TampaHackerspace/SuperHoop/code/SuperHoop_PCB/20131002_133155.jpg

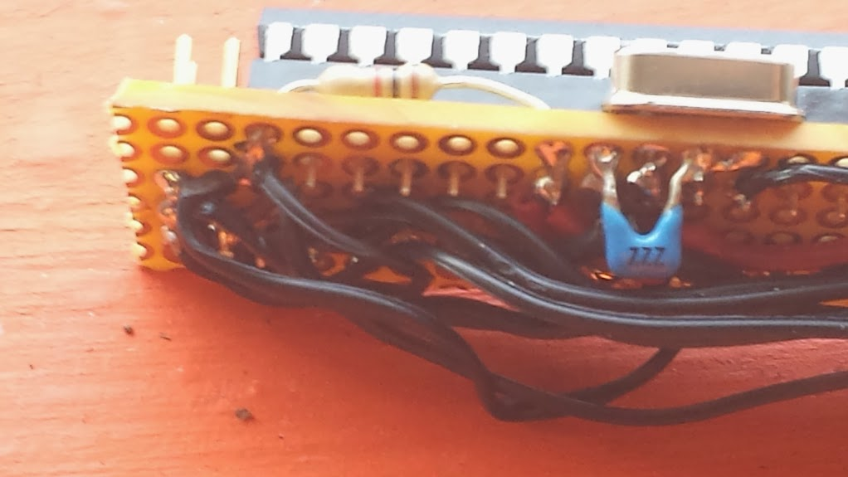
code/SuperHoop_PCB/20131002_133155.jpg
