TampaHackerspace/SuperHoop/code/SuperHoop_PCB/20131002_133200.jpg

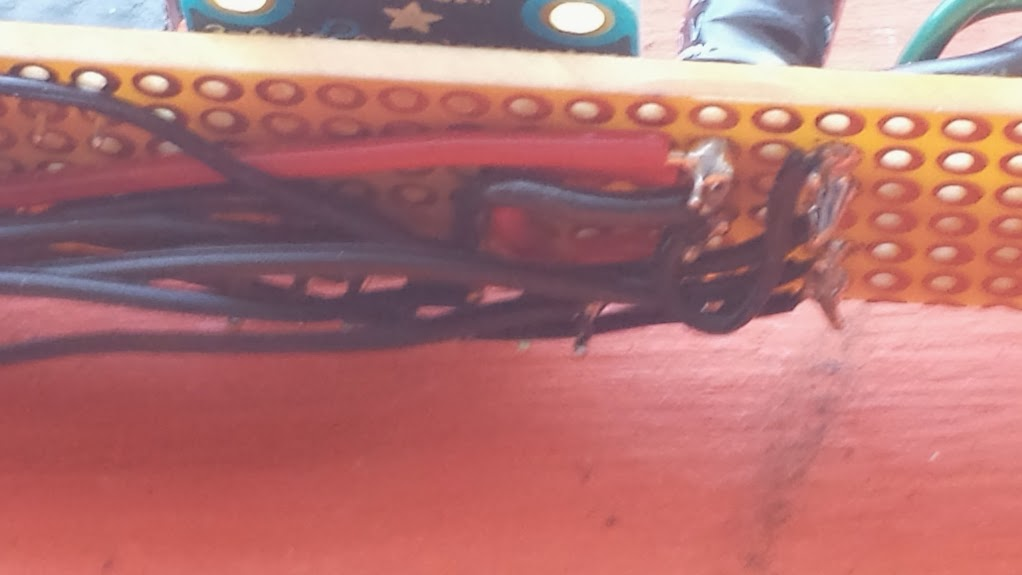
code/SuperHoop_PCB/20131002_133200.jpg
