TampaHackerspace/SuperHoop/code/SuperHoop_PCB/20131002_133217.jpg

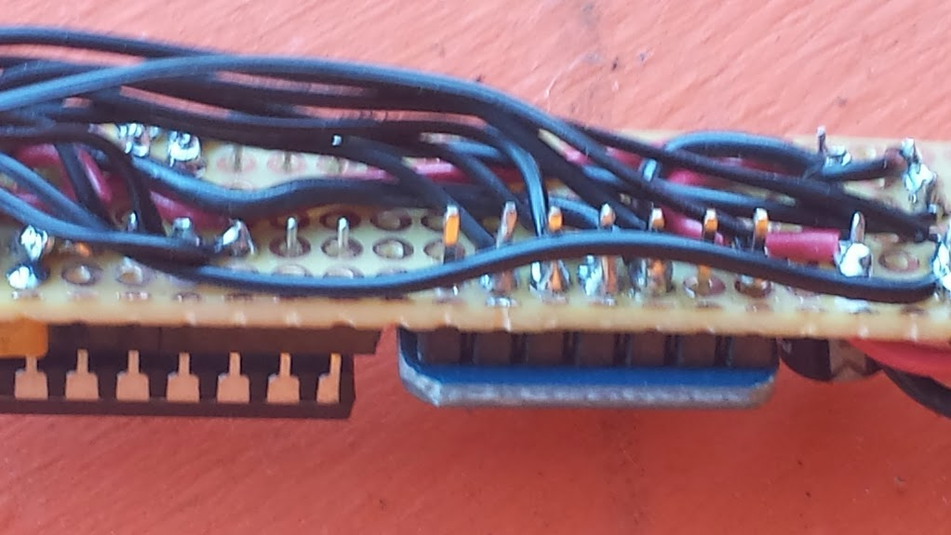
code/SuperHoop_PCB/20131002_133217.jpg
