TampaHackerspace/SuperHoop/code/SuperHoop_PCB/20131002_133244.jpg

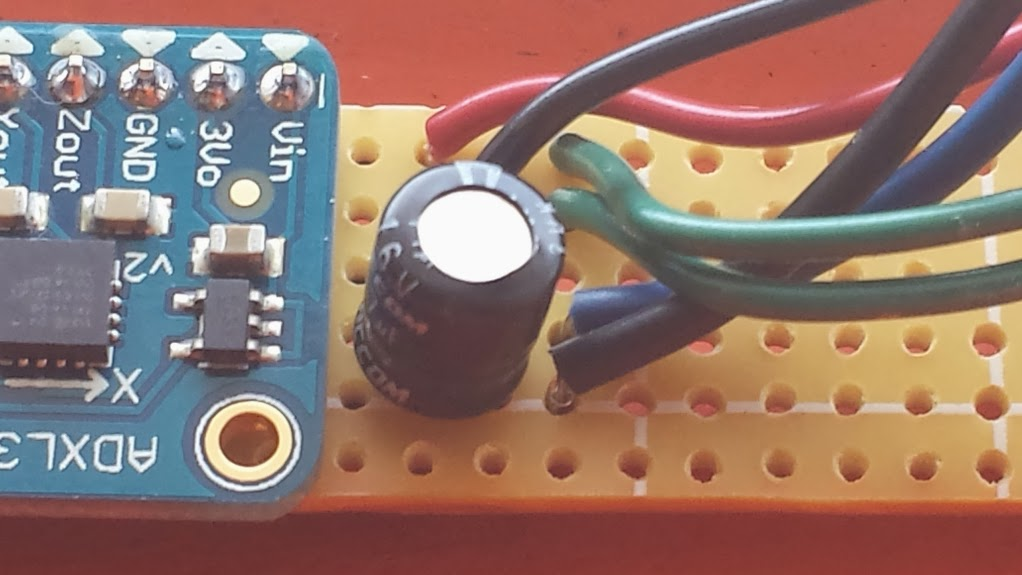
code/SuperHoop_PCB/20131002_133244.jpg
