TampaHackerspace/SuperHoop/code/SuperHoop_PCB/20131002_133307.jpg

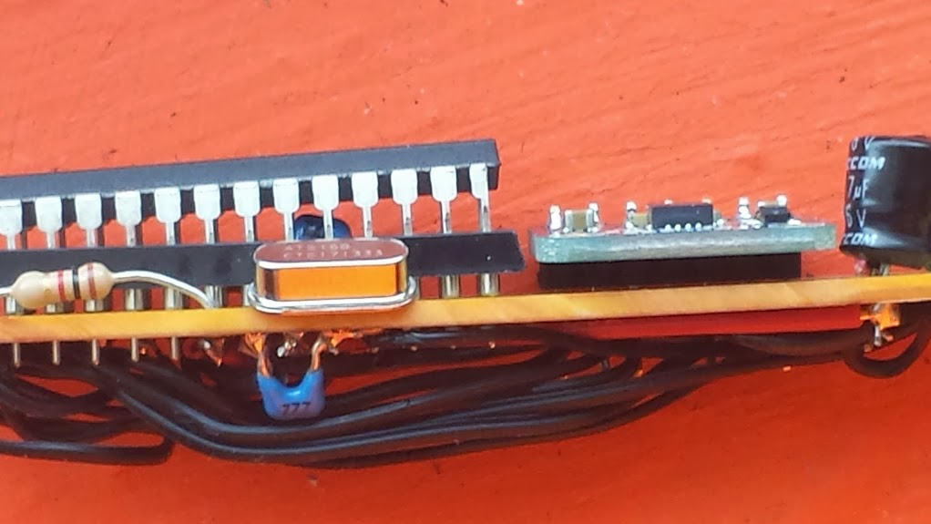
code/SuperHoop_PCB/20131002_133307.jpg
