TampaHackerspace/SuperHoop/code/SuperHoop_PCB/20131002_133337.jpg

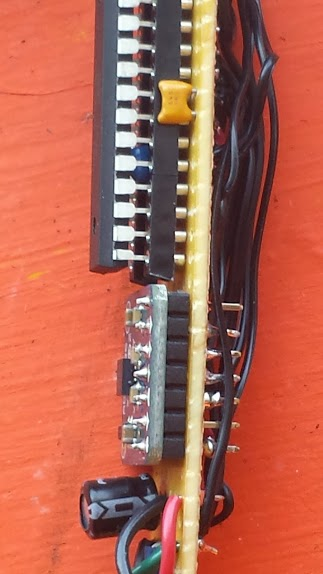
code/SuperHoop_PCB/20131002_133337.jpg
