TampaHackerspace/SuperHoop/code/SuperHoop_PCB/20131002_133351.jpg

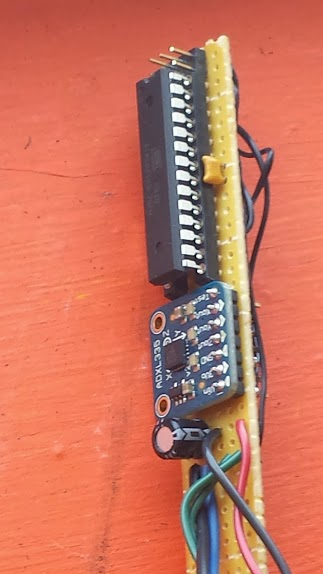
code/SuperHoop_PCB/20131002_133351.jpg
