TampaHackerspace/SuperHoop/code/SuperHoopStrandtest/superHoopStrandTest_show_9pattern/superHoopStrandTest_show_9pattern.ino

#include <Adafruit_NeoPixel.h>

//Code by Andrew Schreiber
// 09-21-2013
//long currentmillis
#define PIN 6//digital out to neopixel strip
#define PIXELS 90
//#define PATTERN_SIZE 18
#define DELAY 15
//r=0x1,0x2, g=0x4,0x8, b=0x10,0x20
#define PATTERN_SIZE 18
#define PATTERN_REPEAT 18
#define NUM_PATTERNS 4

const byte pattern1[PATTERN_SIZE][PATTERN_REPEAT] =
{
  {    00, 00, 00, 00, 00, 00, 00, 00, 52, 00, 00, 00, 00, 00, 00, 00, 00, 00  }  , 
  {    00, 00, 00, 00, 00, 00, 00, 00, 52, 48, 00, 00, 00, 00, 00, 00, 00, 00  }  , 
  {    00, 00, 00, 00, 00, 00, 00, 00, 52, 48, 00, 00, 00, 00, 00, 00, 00, 00  }  , 
  {    00, 00, 00, 00, 00, 00, 00, 00, 52, 48, 60, 00, 00, 00, 00, 00, 00, 00  }  , 
  {    00, 00, 00, 00, 00, 00, 00, 48, 60, 00, 52, 00, 00, 00, 00, 00, 00, 00  }  , 
  {    00, 00, 00, 00, 00, 00, 00, 48, 00, 00, 52, 00, 00, 00, 00, 00, 00, 00  }  , 
  {    00, 00, 00, 00, 00, 00, 60, 48, 00, 00, 52, 60, 00, 00, 00, 00, 00, 00  }  , 
  {    00, 00, 00, 00, 52, 52, 52, 00, 00, 00, 00, 48, 48, 48, 00, 00, 00, 00  }  , 
  {    48, 48, 48, 48, 60, 00, 00, 00, 00, 00, 00, 00, 00, 60, 52, 52, 52, 52  }  , 
  {    00, 52, 52, 52, 00, 00, 00, 00, 00, 00, 00, 00, 00, 00, 48, 48, 48, 00  }  , 
  {    00, 00, 00, 60, 48, 48, 48, 00, 00, 00, 00, 52, 52, 52, 60, 00, 00, 00  }  , 
  {    00, 00, 00, 00, 00, 00, 60, 52, 00, 00, 48, 60, 00, 00, 00, 00, 00, 00  }  , 
  {    00, 00, 00, 00, 00, 00, 00, 52, 00, 00, 48, 00, 00, 00, 00, 00, 00, 00  }  , 
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
{48, 48, 00, 00, 00, 00, 00, 18, 18, 18, 18, 00, 00, 00, 00, 00, 48, 48}, 
{48, 48, 00, 00, 00, 22, 22, 22, 22, 23, 22, 22, 22, 00, 00, 00, 48, 48}, 
{48, 48, 00, 00, 22, 22, 22, 22, 22, 22, 22, 22, 22, 22, 00, 00, 48, 48}, 
{48, 48, 00, 22, 22, 23, 22, 00, 00, 00, 00, 22, 22, 22, 22, 00, 49, 48}, 
{48, 49, 00, 22, 22, 22, 00, 00, 00, 00, 00, 00, 22, 22, 22, 18, 49, 48}, 
{48, 49, 18, 22, 22, 00, 00, 00, 00, 00, 00, 00, 00, 22, 23, 18, 49, 48}, 
{48, 49, 18, 22, 22, 00, 00, 00, 25, 25, 00, 00, 00, 22, 23, 18, 49, 48}, 
{48, 49, 18, 6, 22, 00, 00, 00, 25, 25, 00, 00, 00, 22, 22, 18, 49, 48}, 
{48, 33, 22, 22, 22, 00, 00, 00, 00, 00, 00, 00, 00, 22, 23, 18, 49, 48}, 
{48, 49, 00, 22, 22, 22, 00, 00, 00, 00, 00, 00, 22, 6, 22, 18, 49, 48}, 
{48, 48, 00, 22, 22, 22, 22, 00, 00, 00, 00, 22, 23, 22, 6, 00, 48, 48}, 
{48, 48, 00, 00, 22, 22, 6, 22, 22, 22, 22, 22, 6, 22, 00, 00, 48, 48}, 
{48, 48, 00, 00, 00, 22, 22, 23, 22, 22, 23, 22, 22, 00, 00, 00, 48, 48}, 
{48, 48, 00, 00, 00, 00, 18, 18, 18, 18, 18, 18, 00, 00, 00, 00, 48, 48}, 
{48, 48, 48, 48, 48, 49, 49, 49, 49, 49, 49, 49, 48, 48, 48, 48, 48, 48}, 
{48, 48, 48, 48, 48, 48, 48, 48, 48, 48, 48, 48, 48, 48, 48, 48, 48, 48}};


// Parameter 1 = number of pixels in strip
// Parameter 2 = pin number (most are valid)
// Parameter 3 = pixel type flags, add together as needed:
//   NEO_KHZ800  800 KHz bitstream (most NeoPixel products w/WS2812 LEDs)
//   NEO_KHZ400  400 KHz (classic 'v1' (not v2) FLORA pixels, WS2811 drivers)
//   NEO_GRB     Pixels are wired for GRB bitstream (most NeoPixel products)
//   NEO_RGB     Pixels are wired for RGB bitstream (v1 FLORA pixels, not v2)

Adafruit_NeoPixel strip = Adafruit_NeoPixel(90, PIN, NEO_GRB + NEO_KHZ800);
int frame = 0;
int currentPattern = 0;
int counter=0;
void setup() {

  strip.begin();
  strip.show(); // Initialize all pixels to 'off'

}



void loop() {
  // Some example procedures showing how to display to the pixels:
  //currentmillis=millis();
  render_frame(frame);
  frame++;
  frame = frame%PATTERN_REPEAT;
  delay(DELAY);
  counter++;
  if(counter>1000)
  {
    counter=0;
    currentPattern++;
    currentPattern = currentPattern%NUM_PATTERNS;
  }
}

void render_frame(int frame)
{
  //Serial.println("BLA");
  for(int i=0;i<18;i++)
  {
    //Serial.println(i);
    for(int offset=0; offset < PIXELS; offset+=PATTERN_SIZE){
      switch (currentPattern){
      case 0:
        strip.setPixelColor(i+offset,replaceColor(pattern1[frame][i]));
        break;
      case 1:
        strip.setPixelColor(i+offset,replaceColor(pattern2[frame][i]));
        break;
      case 2:
        strip.setPixelColor(i+offset,replaceColor(pattern3[frame][i]));
        break;
      case 3:
        strip.setPixelColor(i+offset,replaceColor(pattern4[frame][i]));
        break;
      }
    }
  }
  strip.show(); // push out to strip

}

unsigned long replaceColor(byte color)//extend 2 bits to 24 and shift bits for brighter shades
{
  byte redcolor=0;
  byte grncolor=0;
  byte blucolor=0;
  switch (color&0x03){//red{//mask off the 2 relevant bits and expand to 8 bits
  case 0x01:
    redcolor=0x3F;
    break;
  case 0x02:
    redcolor=0xC0;
    break;
  case 0x03:
    redcolor=0xFF;
    break;
  default:
    redcolor=0x00;
  }
  switch (color&0x0C){//grn{
  case 0x04:
    grncolor=0x3F;
    break;
  case 0x08:
    grncolor=0xC0;
    break;
  case 0x0C:
    grncolor=0xFF;
    break;
  default:
    grncolor=0x00;
  }
  switch (color&0x30){//blu{
  case 0x10:
    blucolor=0x3F;
    break;
  case 0x20:
    blucolor=0xC0;
    break;
  case 0x30:
    blucolor=0xFF;
    break;
  default:
    blucolor=0x00;
  }

  return strip.Color(redcolor,  grncolor,  blucolor);//combine individual 8 bit RGB values to a long
}
